Blureo/POV-Clock/C-files/POVDisplay.cpp

#include "POVDisplay.h"
#include <MKL16Z4.h>
#include <stdint.h>
#include "DLED.h"

POVDisplay::POVDisplay()
{
}

void POVDisplay::Init()
{
	SIM->SCGC6 |= (SIM_SCGC6_PIT_MASK);
	PIT->MCR = (PIT->MCR & ~PIT_MCR_MDIS_MASK);
	PIT->CHANNEL[0].LDVAL = 1398;// 14MHZ clock frequency
	PIT->CHANNEL[0].TCTRL = (PIT->CHANNEL[0].TCTRL & ~PIT_TCTRL_TEN_MASK) | PIT_TCTRL_TEN_MASK;
	PIT->CHANNEL[0].TCTRL = (PIT->CHANNEL[0].TCTRL & ~PIT_TCTRL_TIE_MASK) | PIT_TCTRL_TIE_MASK;
	NVIC_EnableIRQ(PIT_IRQn);

}

void POVDisplay::setDisplayTemp(int Temperature)
{
	int temp[3];
	temp[2] = (Temperature%10) ;// ones digit for Temperature
	Temperature = Temperature/10;
	temp[1] = (Temperature%10) ; // tens digit for Temperature
	Temperature = Temperature/10;
	temp[0] = (Temperature%10) ;// hundreds digit for Temperature
	bookmark = 0;
	if (temp[0]== 0) // if statment when hundreds digit is 0 is not needed to be displaied
	{
		for(int i = 1; i < 3; i++) // tens and ones are put in buffer
		{
			for(int j = fontIndexPOV[temp[i]]; j < (fontIndexPOV[temp[i]+1]); j++) // loop that calls index to find the frist and last part of the pattern for the digit
			{
				g_displaybuff[bookmark] = font[j]; // puts the current pattern into a buffer
				bookmark++; // bookmark to track how long lenght is
			}
			for(int j = 0; j < 4; j++) // use to added space between numbers
			{
				g_displaybuff[bookmark] = 0x0;
				bookmark++;
			}
		}
	}
	else // when hunders is not 0 this loop is called
	{
		for(int i = 0; i < 3; i++)// loop from 3 digit
		{
			for(int j = fontIndexPOV[temp[i]]; j < (fontIndexPOV[temp[i]+1]); j++) // loop that calls index to find the frist and last part of the pattern for the digit 
			{
				g_displaybuff[bookmark] = font[j]; // addes pattern into buffer
				bookmark++;
			}
			for(int j = 0; j < 4; j++)
			{
				g_displaybuff[bookmark] = 0x0; // use to added space between numbers 
				bookmark++;
			}
		}
	}
	
	for(int j = fontIndexPOV[14]; j < (fontIndexPOV[15]); j++)
	{
		g_displaybuff[bookmark] = font[j];
		bookmark++;
	}
	for(int j = 0; j < 4; j++)
		{
			g_displaybuff[bookmark] = 0x0;
			bookmark++;
		}
	for(int j = fontIndexPOV[12]; j < (fontIndexPOV[13]); j++)
	{
		g_displaybuff[bookmark] = font[j];
		bookmark++;
	}
	for(int j = 0; j < 20; j++)
		{
			g_displaybuff[bookmark] = 0x0;
			bookmark++;
		}
	displaycounter = bookmark;

} // end setDisplayTemp

void POVDisplay::setDisplayTime(int Time)
{
	
	bookmark = 0;
	int tempbuff[4];
	tempbuff[3] = (Time%10) ;// ones digit for minutes
	Time = Time/10;
	tempbuff[2] = (Time%10) ; // tens digit for miunrs
	Time = Time/10;
	tempbuff[1] = (Time%10) ;// ones digit for hours
	Time = Time/10;
	tempbuff[0] = (Time%10) ;// tens digit for hours
	
	for(int i = 0; i < 2; i++)// loop from 3 digit
		{
			for(int j = fontIndexPOV[tempbuff[i]]; j < (fontIndexPOV[tempbuff[i]+1]); j++) // loop that calls index to find the frist and last part of the pattern for the digit 
			{
				g_displaybuff[bookmark] = font[j]; // addes pattern into buffer
				bookmark++;
			}
			for(int j = 0; j < 5; j++)
			{
				g_displaybuff[bookmark] = 0x0; // use to added space between numbers 
				bookmark++;
			}
		}
		for(int j = fontIndexPOV[10]; j < (fontIndexPOV[11]); j++) // loop that calls index to find the frist and last part of the pattern for the digit 
		{
			g_displaybuff[bookmark] = font[j]; // addes pattern into buffer
			bookmark++;
		}
		for(int j = 0; j < 5; j++)
		{
			g_displaybuff[bookmark] = 0x0; // use to added space between numbers 
			bookmark++;
		}
		for(int i = 2; i < 4; i++)// loop from 3 digit
		{
			for(int j = fontIndexPOV[tempbuff[i]]; j < (fontIndexPOV[tempbuff[i]+1]); j++) // loop that calls index to find the frist and last part of the pattern for the digit 
			{
				g_displaybuff[bookmark] = font[j]; // addes pattern into buffer
				bookmark++;
			}
			for(int j = 0; j < 10; j++)
			{
				g_displaybuff[bookmark] = 0x0; // use to added space between numbers 
				bookmark++;
			}
		}
		for(int j = 0; j < 20; j++)
		{
			g_displaybuff[bookmark] = 0x0;
			bookmark++;
		}
	displaycounter = bookmark;
}// end setDisplayTime
void POVDisplay::Display()
{
	g_DLED.UpdateLED(g_displaybuff[displaycounter]);
	
	if (displaycounter == bookmark)
	{
		displaycounter = 0;
	}
	displaycounter++;
}

const int16_t POVDisplay::fontIndexPOV[NUM_FONT_INDEX_TABLE_ENTRIES] = {
	148,  // 0 (ASCII 48)
  166,  // 1 (ASCII 49)
  176,  // 2 (ASCII 50)
  193,  // 3 (ASCII 51)
  210,  // 4 (ASCII 52)
  229,  // 5 (ASCII 53)
  247,  // 6 (ASCII 54)
  264,  // 7 (ASCII 55)
  281,  // 8 (ASCII 56)
  298,  // 9 (ASCII 57)
  315,  // : (ASCII 58)
	320,  // < (ASCII 60)
	517,  // F (ASCII 70)
	532,  // G (ASCII 71)
	1362,  // ? (ASCII 176)
	1373  // ? (ASCII 177)
	
};

const uint16_t POVDisplay::font[] = {
  0x0000, 0x200c, 0x3fcc, 0x3fcc, 0x3fcc, 0x300c, 0x0040, 0x0040, 0x0444, 0x045c,
  0x047c, 0x05f8, 0x07c0, 0x1f40, 0x3c40, 0x3c44, 0x245c, 0x047c, 0x04f8, 0x07e0,
  0x0fc0, 0x1e40, 0x3c40, 0x3440, 0x2440, 0x0400, 0x0400, 0x0610, 0x0f30, 0x0f30,
  0x1f38, 0x1998, 0x1998, 0x1988, 0x3ffe, 0x3ffe, 0x3ffe, 0x1898, 0x18d8, 0x1cf8,
  0x0cf0, 0x0c70, 0x0460, 0x0e00, 0x1f00, 0x1f00, 0x3f80, 0x3180, 0x2080, 0x2080,
  0x2080, 0x3180, 0x3f84, 0x1f0c, 0x1f1c, 0x0e38, 0x0070, 0x00e0, 0x01c0, 0x03c0,
  0x0380, 0x0700, 0x0e00, 0x1c70, 0x38f8, 0x30f8, 0x21fc, 0x018c, 0x0104, 0x0104,
  0x0104, 0x018c, 0x01fc, 0x00f8, 0x00f8, 0x0070, 0x0070, 0x0078, 0x00f8, 0x1cf8,
  0x1ecc, 0x3f8c, 0x3f8c, 0x378c, 0x238c, 0x238c, 0x23cc, 0x36ec, 0x3eec, 0x3e7c,
  0x1c38, 0x1838, 0x003c, 0x00fc, 0x00fc, 0x00e4, 0x0084, 0x0000, 0x00c0, 0x00c0,
  0x00c0, 0x00c0, 0x00c0, 0x00c0, 0x00c0, 0x00c0, 0x0ffc, 0x0ffc, 0x0ffc, 0x00c0,
  0x00c0, 0x00c0, 0x00c0, 0x00c0, 0x00c0, 0x00c0, 0x00c0, 0x00c0, 0x00c0, 0x00c0,
  0x00c0, 0x00c0, 0x00c0, 0x00c0, 0x00c0, 0x00c0, 0x00c0, 0x000c, 0x000c, 0x000c,
  0x000c, 0x000c, 0x0000, 0x0001, 0x0003, 0x000f, 0x001f, 0x003e, 0x0078, 0x01f0,
  0x03e0, 0x0780, 0x1f00, 0x3e00, 0x7c00, 0x7000, 0x6000, 0x4000, 0x07e0, 0x0ff0,
  0x1ff8, 0x1ff8, 0x3c3c, 0x381c, 0x300c, 0x300c, 0x300c, 0x300c, 0x300c, 0x300c,
  0x381c, 0x3c3c, 0x1ff8, 0x1ff8, 0x0ff0, 0x07e0, 0x0800, 0x0800, 0x0800, 0x0800,
  0x0800, 0x1800, 0x1ffc, 0x3ffc, 0x3ffc, 0x3ffc, 0x080c, 0x101c, 0x181c, 0x381c,
  0x303c, 0x303c, 0x307c, 0x306c, 0x30ec, 0x30cc, 0x31cc, 0x3b8c, 0x3f8c, 0x1f0c,
  0x1f0c, 0x0e0c, 0x000c, 0x0008, 0x1008, 0x1818, 0x381c, 0x300c, 0x300c, 0x318c,
  0x318c, 0x318c, 0x318c, 0x318c, 0x318c, 0x3bdc, 0x3ff8, 0x1ef8, 0x1e78, 0x0c70,
  0x0030, 0x0070, 0x00f0, 0x00f0, 0x01f0, 0x03b0, 0x0330, 0x0730, 0x0e30, 0x0c30,
  0x1c30, 0x3830, 0x3ffc, 0x3ffc, 0x3ffc, 0x3ffc, 0x0030, 0x0030, 0x0030, 0x0008,
  0x0308, 0x1f18, 0x3f1c, 0x3f0c, 0x3b0c, 0x330c, 0x330c, 0x330c, 0x330c, 0x330c,
  0x330c, 0x330c, 0x339c, 0x31f8, 0x31f8, 0x31f0, 0x00e0, 0x03e0, 0x07f0, 0x0ff8,
  0x1ff8, 0x1d3c, 0x391c, 0x330c, 0x330c, 0x330c, 0x330c, 0x330c, 0x330c, 0x339c,
  0x3bf8, 0x11f8, 0x11f0, 0x00f0, 0x3000, 0x3000, 0x3000, 0x3000, 0x3004, 0x300c,
  0x301c, 0x303c, 0x307c, 0x31f8, 0x33f0, 0x37c0, 0x3f80, 0x3f00, 0x3e00, 0x3800,
  0x3000, 0x0070, 0x0c78, 0x1ef8, 0x1efc, 0x3fcc, 0x338c, 0x338c, 0x318c, 0x318c,
  0x318c, 0x338c, 0x338c, 0x3fcc, 0x1efc, 0x1ef8, 0x0c78, 0x0030, 0x0e00, 0x1f08,
  0x1f08, 0x1f9c, 0x3b8c, 0x318c, 0x318c, 0x318c, 0x318c, 0x318c, 0x318c, 0x319c,
  0x3df8, 0x1ff8, 0x1ff0, 0x0ff0, 0x07c0, 0x060c, 0x060c, 0x060c, 0x060c, 0x060c,
  0x00c0, 0x00c0, 0x01c0, 0x01c0, 0x01c0, 0x0160, 0x0160, 0x0360, 0x0320, 0x0330,
  0x0330, 0x0230, 0x0610, 0x0618, 0x0618, 0x0618, 0x0408, 0x0c08, 0x0c0c, 0x0c0c,
  0x0330, 0x0330, 0x0330, 0x0330, 0x0330, 0x0330, 0x0330, 0x0330, 0x0330, 0x0330,
  0x0330, 0x0330, 0x0330, 0x0330, 0x0330, 0x0330, 0x0330, 0x0330, 0x0330, 0x0c0c,
  0x0c0c, 0x0c08, 0x0408, 0x0618, 0x0618, 0x0618, 0x0610, 0x0230, 0x0330, 0x0330,
  0x0320, 0x0360, 0x0160, 0x0160, 0x01c0, 0x01c0, 0x01c0, 0x00c0, 0x00c0, 0x0800,
  0x1000, 0x1800, 0x3800, 0x3000, 0x30ec, 0x30ec, 0x30ec, 0x30ec, 0x318c, 0x3180,
  0x3b80, 0x3f00, 0x1f00, 0x1e00, 0x0e00, 0x01f0, 0x03f8, 0x07fc, 0x071e, 0x0e06,
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
};
